Arthrimus/Saturn_Controller_Demux/saturn_controller_demux_v0.1_board/saturn_controller_demux_v0.1_board.ino

 /* Saturn Controller Demux
 * ------------------ 
 * This sketch is designed to demux Sega Saturn gamepad
 * signals into descrete outputs for use with arcade 
 * PCBs. 
 * 
 * There are two select lines, four data input lines, and
 * 13 discrete outputs. The controlls can be remapped by 
 * changing the pin assignments below.
 * 
 * Appollogies for the sloppy code. It took a lot of trial and error
 * to get all the timings right for MC Cthulu boards to work properly
 * I tried to clean it up as much as I could.
 * 
 * Arthrimus December 24 2018
 *
 */

int UP = 13; // These choose the pins for the button outputs. (Change these
int DN = 12; // if you wish to remap the buttons.)
int LT = 11;
int RT = 10;
int A = 6;
int B = 1;
int C = 4;
int X = 9;
int Y = 8;
int Z = 7;
int L = 3;
int R = 2;
int ST = 5;   
int D0 = 15;  // choose the input pins for the digital lines (Probably don't change these)
int D1 = 14;
int D2 = 19;
int D3 = 18;
int S0 = 16; // Chooses the output pins for the select lines (Probably don't change these either)
int S1 = 17;
int val = 0;     // variable for reading the pin status (should be zero)

void setup() {
  pinMode(UP, OUTPUT);  // declares buttons as outputs (don't change these)
  pinMode(DN, OUTPUT); 
  pinMode(LT, OUTPUT);
  pinMode(RT, OUTPUT);
  pinMode(A, OUTPUT);
  pinMode(B, OUTPUT);
  pinMode(C, OUTPUT);
  pinMode(X, OUTPUT);
  pinMode(Y, OUTPUT);
  pinMode(Z, OUTPUT);
  pinMode(L, OUTPUT);
  pinMode(R, OUTPUT);
  pinMode(ST,OUTPUT);
  pinMode(D0, INPUT_PULLUP);    // declare pushbutton as input (or these)
  pinMode(D1, INPUT_PULLUP);
  pinMode(D2, INPUT_PULLUP);
  pinMode(D3, INPUT_PULLUP);
  pinMode(S0, OUTPUT); // Declare Select Pins as outputs (these either)
  pinMode(S1, OUTPUT);
}

void loop(){
  
  {                             // This is the start of the first bit of the demuxer, there are four of these
  delay(5);
  digitalWrite(S1, LOW);
  digitalWrite(S0, HIGH); // Sets the select lines S0 HIGH, S1 LOW
 
  }
  val = digitalRead(D0);  // read input value from data line
  if (val == HIGH) {         // check if the data input is HIGH (button released)
    digitalWrite(B, HIGH);  // Button output is high
  } else {
    digitalWrite(B, LOW);  // Button output is low
  }
  val = digitalRead(D1); 
  if (val == HIGH) {      
    digitalWrite(C, HIGH); 
  } else {
    digitalWrite(C, LOW); 
  }
  val = digitalRead(D2);
  if (val == HIGH) {       
    digitalWrite(A, HIGH);  
  } else {
    digitalWrite(A, LOW);  
  }
  val = digitalRead(D3); 
  if (val == HIGH) {      
    digitalWrite(ST, HIGH);  
  } else {
    digitalWrite(ST, LOW);       
  }                                // This is the end of the first bit of the demuxer.

{                               // This is the start of the second bit of the demuxer.
  delay(5);
  digitalWrite(S1, LOW);           // Sets the select lines S0 LOW, S1 LOW
  digitalWrite(S0, LOW);         
  }
    val = digitalRead(D0);
  if (val == HIGH) {       
    digitalWrite(Z, HIGH); 
  } else {
    digitalWrite(Z, LOW); 
  }
  val = digitalRead(D1); 
  if (val == HIGH) {      
    digitalWrite(Y, HIGH); 
  } else {
    digitalWrite(Y, LOW); 
  }
  val = digitalRead(D2);
  if (val == HIGH) {       
    digitalWrite(X, HIGH);  
  } else {
    digitalWrite(X, LOW);  
  }
  val = digitalRead(D3); 
  if (val == HIGH) {      
    digitalWrite(R, HIGH);  
  } else {
    digitalWrite(R, LOW); 
  }                             // This is the end of the second bit of the demuxer.       
          { 
  delay(5);                    // This is the start of the third bit of the demuxer.
  digitalWrite(S1, HIGH);       // Sets the select lines S0 HIGH, S1 HIGH
  digitalWrite(S0, HIGH);  

  }
  val = digitalRead(D3); 
  if (val == HIGH) {      
    digitalWrite(L, HIGH);  
  } else {
    digitalWrite(L, LOW); 
  }                            // This is the end of the third bit of the demuxer. 
   {                       // This is the start of the fourth bit of the demuxer.
  delay(5);
  digitalWrite(S1, HIGH);// Sets the select lines S0 LOW, S1 HIGH
  digitalWrite(S0, LOW);   

  }
    val = digitalRead(D0); 
  if (val == HIGH) {       
    digitalWrite(UP, HIGH);
  } else {
    digitalWrite(UP, LOW); 
  }
  val = digitalRead(D1); 
  if (val == HIGH) {      
    digitalWrite(DN, HIGH); 
  } else {
    digitalWrite(DN, LOW); 
  }
  val = digitalRead(D2);
  if (val == HIGH) {       
    digitalWrite(LT, HIGH);  
  } else {
    digitalWrite(LT, LOW);  
  }
  val = digitalRead(D3); 
  if (val == HIGH) {      
    digitalWrite(RT, HIGH);  
  } else {
    digitalWrite(RT, LOW);
  }                         // This is the end of the fourth bit of the demuxer. 
  }        // End of the program.
